PaavoHietala/LineFollower/Solidworks/wheel_back_left.SLDPRT

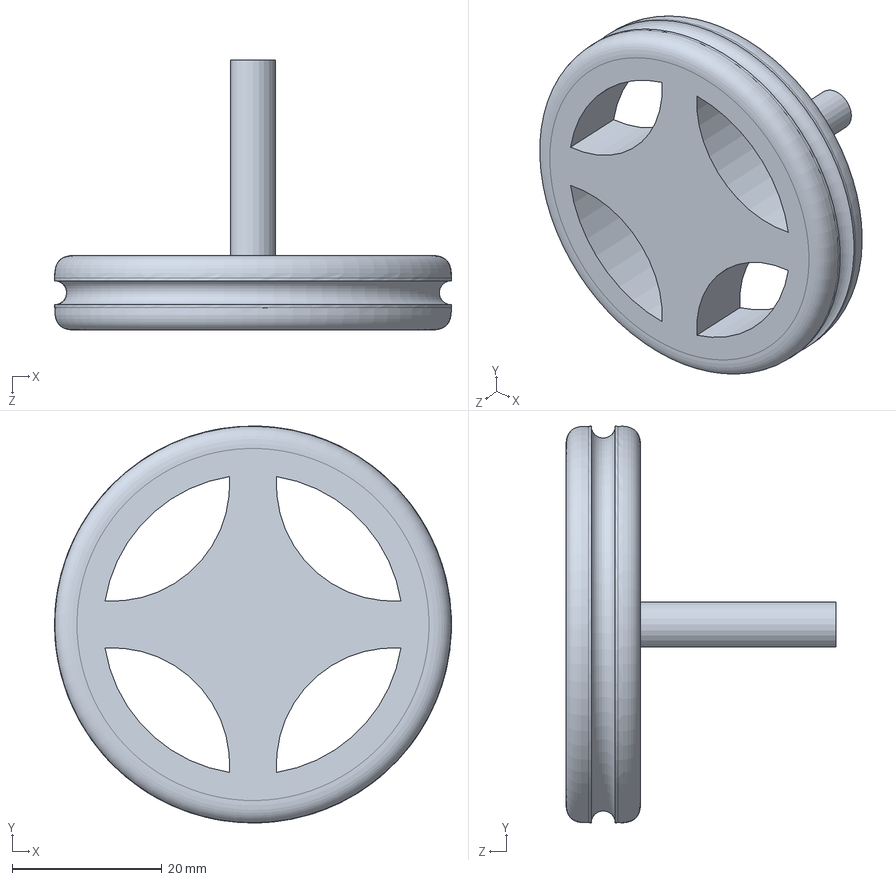
[picture p16: CAD file, 2022-01-27]
Solidworks/wheel_back_left.SLDPRT
53.0 x 53.0 x 36.1 mm
