PaavoHietala/LineFollower/Solidworks/motor_hinge.SLDPRT

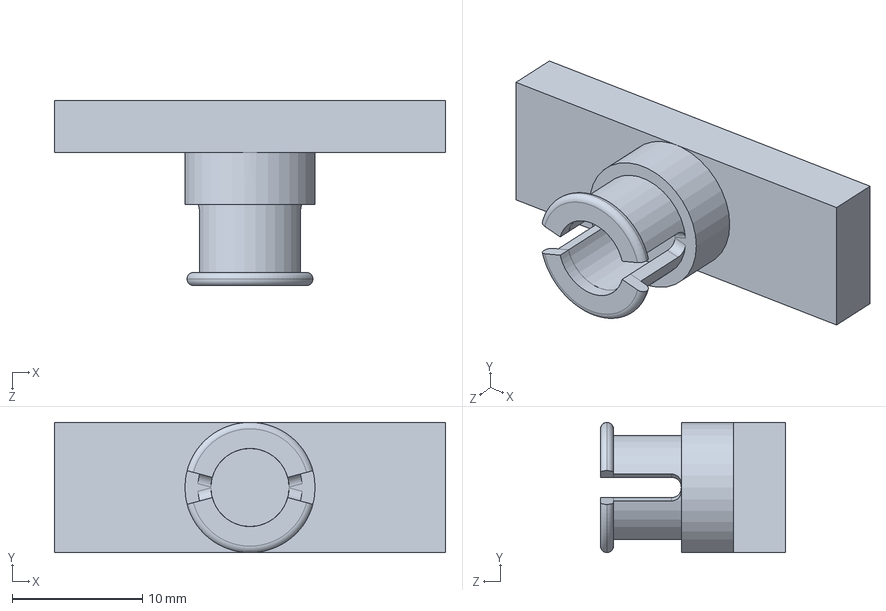
[picture p17: CAD file, 2022-01-25]
Solidworks/motor_hinge.SLDPRT
30.0 x 10.00 x 14.2 mm
