PaavoHietala/LineFollower/Solidworks/motor_holder.SLDPRT

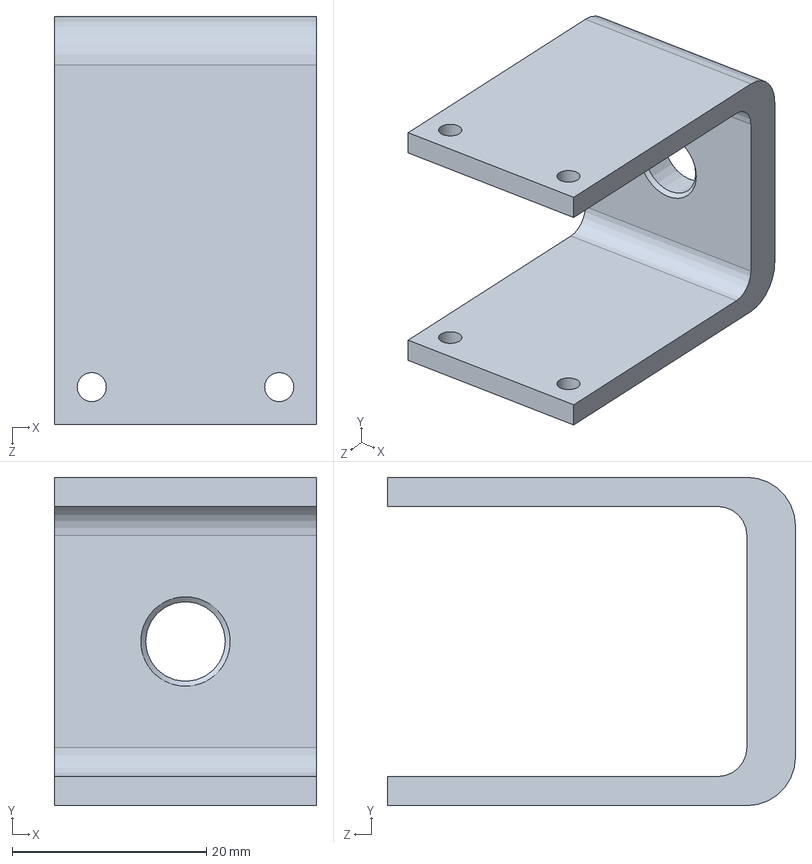
[picture p18: CAD file, 2022-01-25]
Solidworks/motor_holder.SLDPRT
27.0 x 33.8 x 42.0 mm
