PaavoHietala/LineFollower/Solidworks/motor.SLDPRT

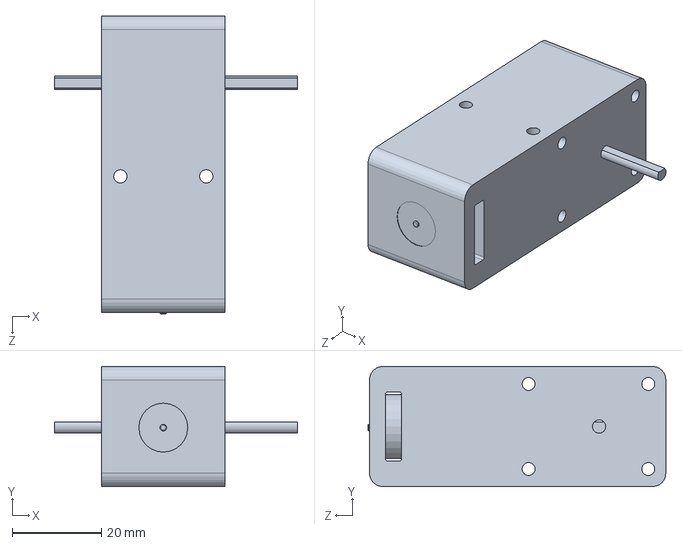
[picture p19: CAD file, 2022-01-25]
Solidworks/motor.SLDPRT
54.6 x 27.0 x 66.9 mm
