PaavoHietala/LineFollower/Solidworks/o-ring.SLDPRT

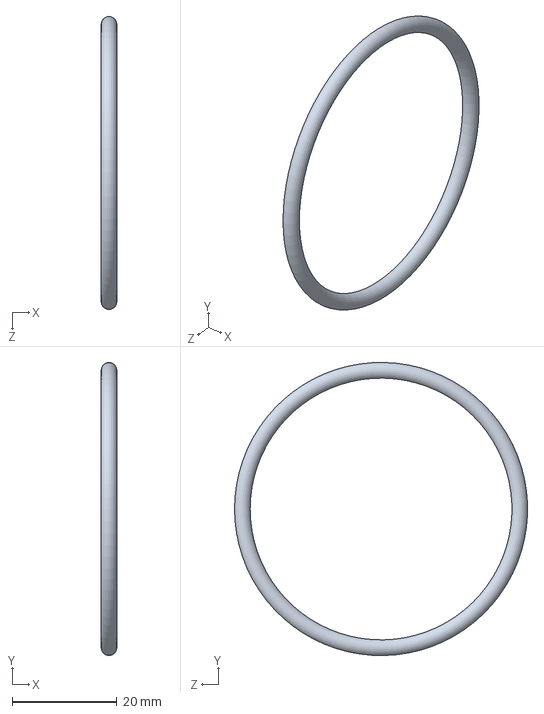
[picture p20: CAD file, 2022-01-25]
Solidworks/o-ring.SLDPRT
3.00 x 56.0 x 56.0 mm
