PaavoHietala/LineFollower/Solidworks/wheel.SLDPRT

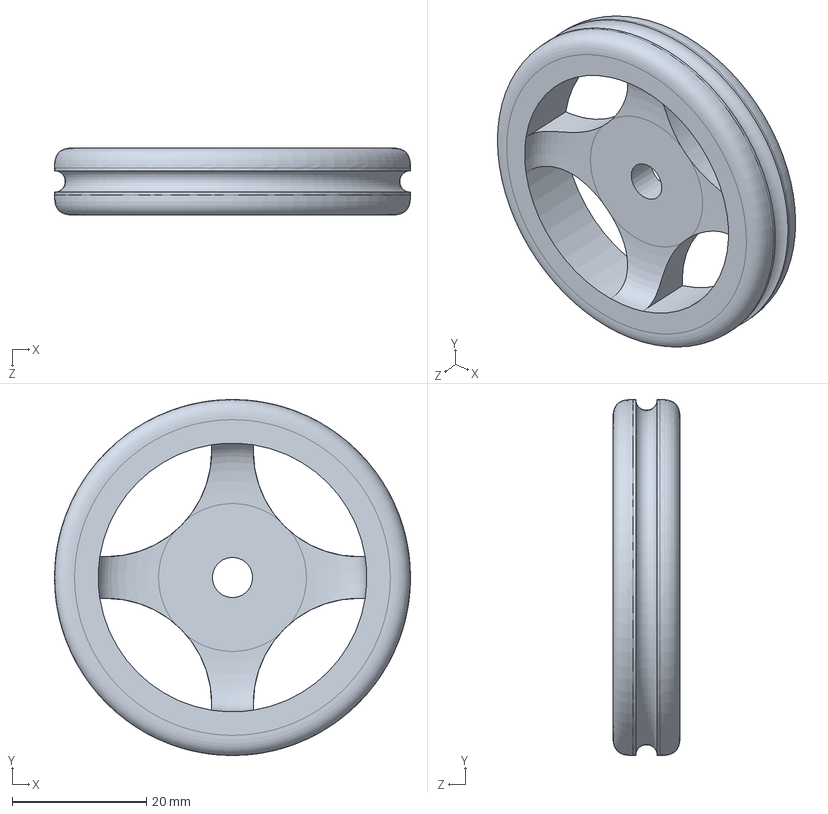
[picture p21: CAD file, 2022-01-25]
Solidworks/wheel.SLDPRT
53.0 x 53.0 x 10.0 mm
