PaavoHietala/LineFollower/Solidworks/front_axle_left_mirror.SLDPRT

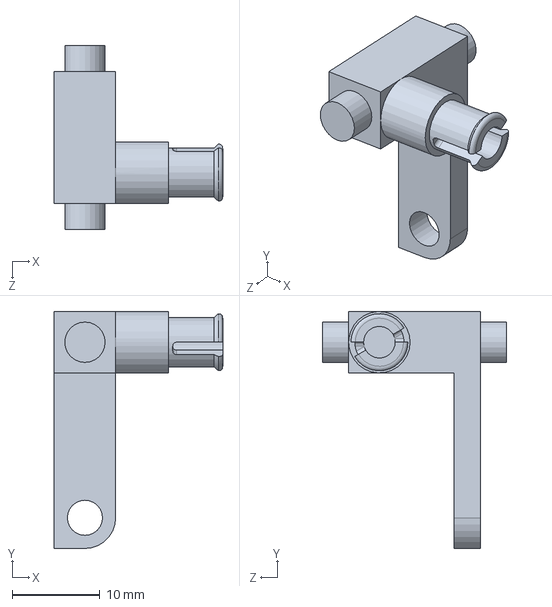
[picture p22: CAD file, 2022-01-17]
Solidworks/front_axle_left_mirror.SLDPRT
19.2 x 27.0 x 21.0 mm
