PaavoHietala/LineFollower/Solidworks/User Library-corpo TCRT 5000.sldprt

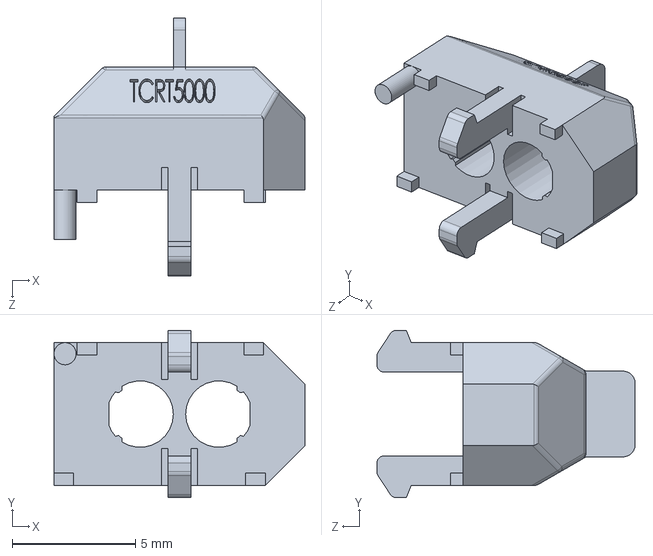
[picture p23: CAD file, 2022-01-07]
Solidworks/User Library-corpo TCRT 5000.sldprt
10.2 x 6.80 x 10.5 mm
