PaavoHietala/LineFollower/Solidworks/Arduino Mega 2560.SLDPRT

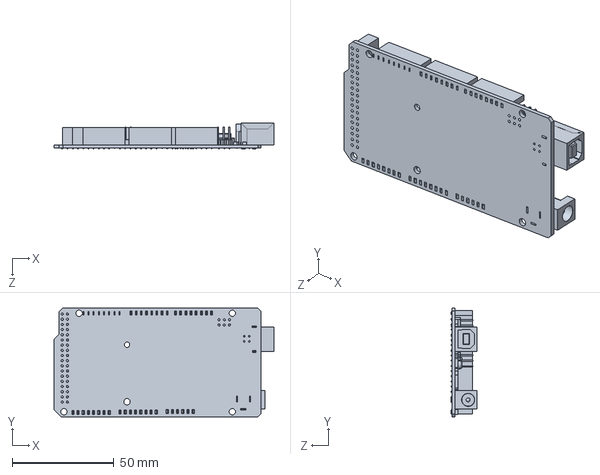
[picture p24: CAD file, 2022-01-07]
Solidworks/Arduino Mega 2560.SLDPRT
107.9 x 53.4 x 13.0 mm
